User330639/ESP_SENSOR_STATION_REV1/HW/OUT/ASM/ASM_Top.PDF

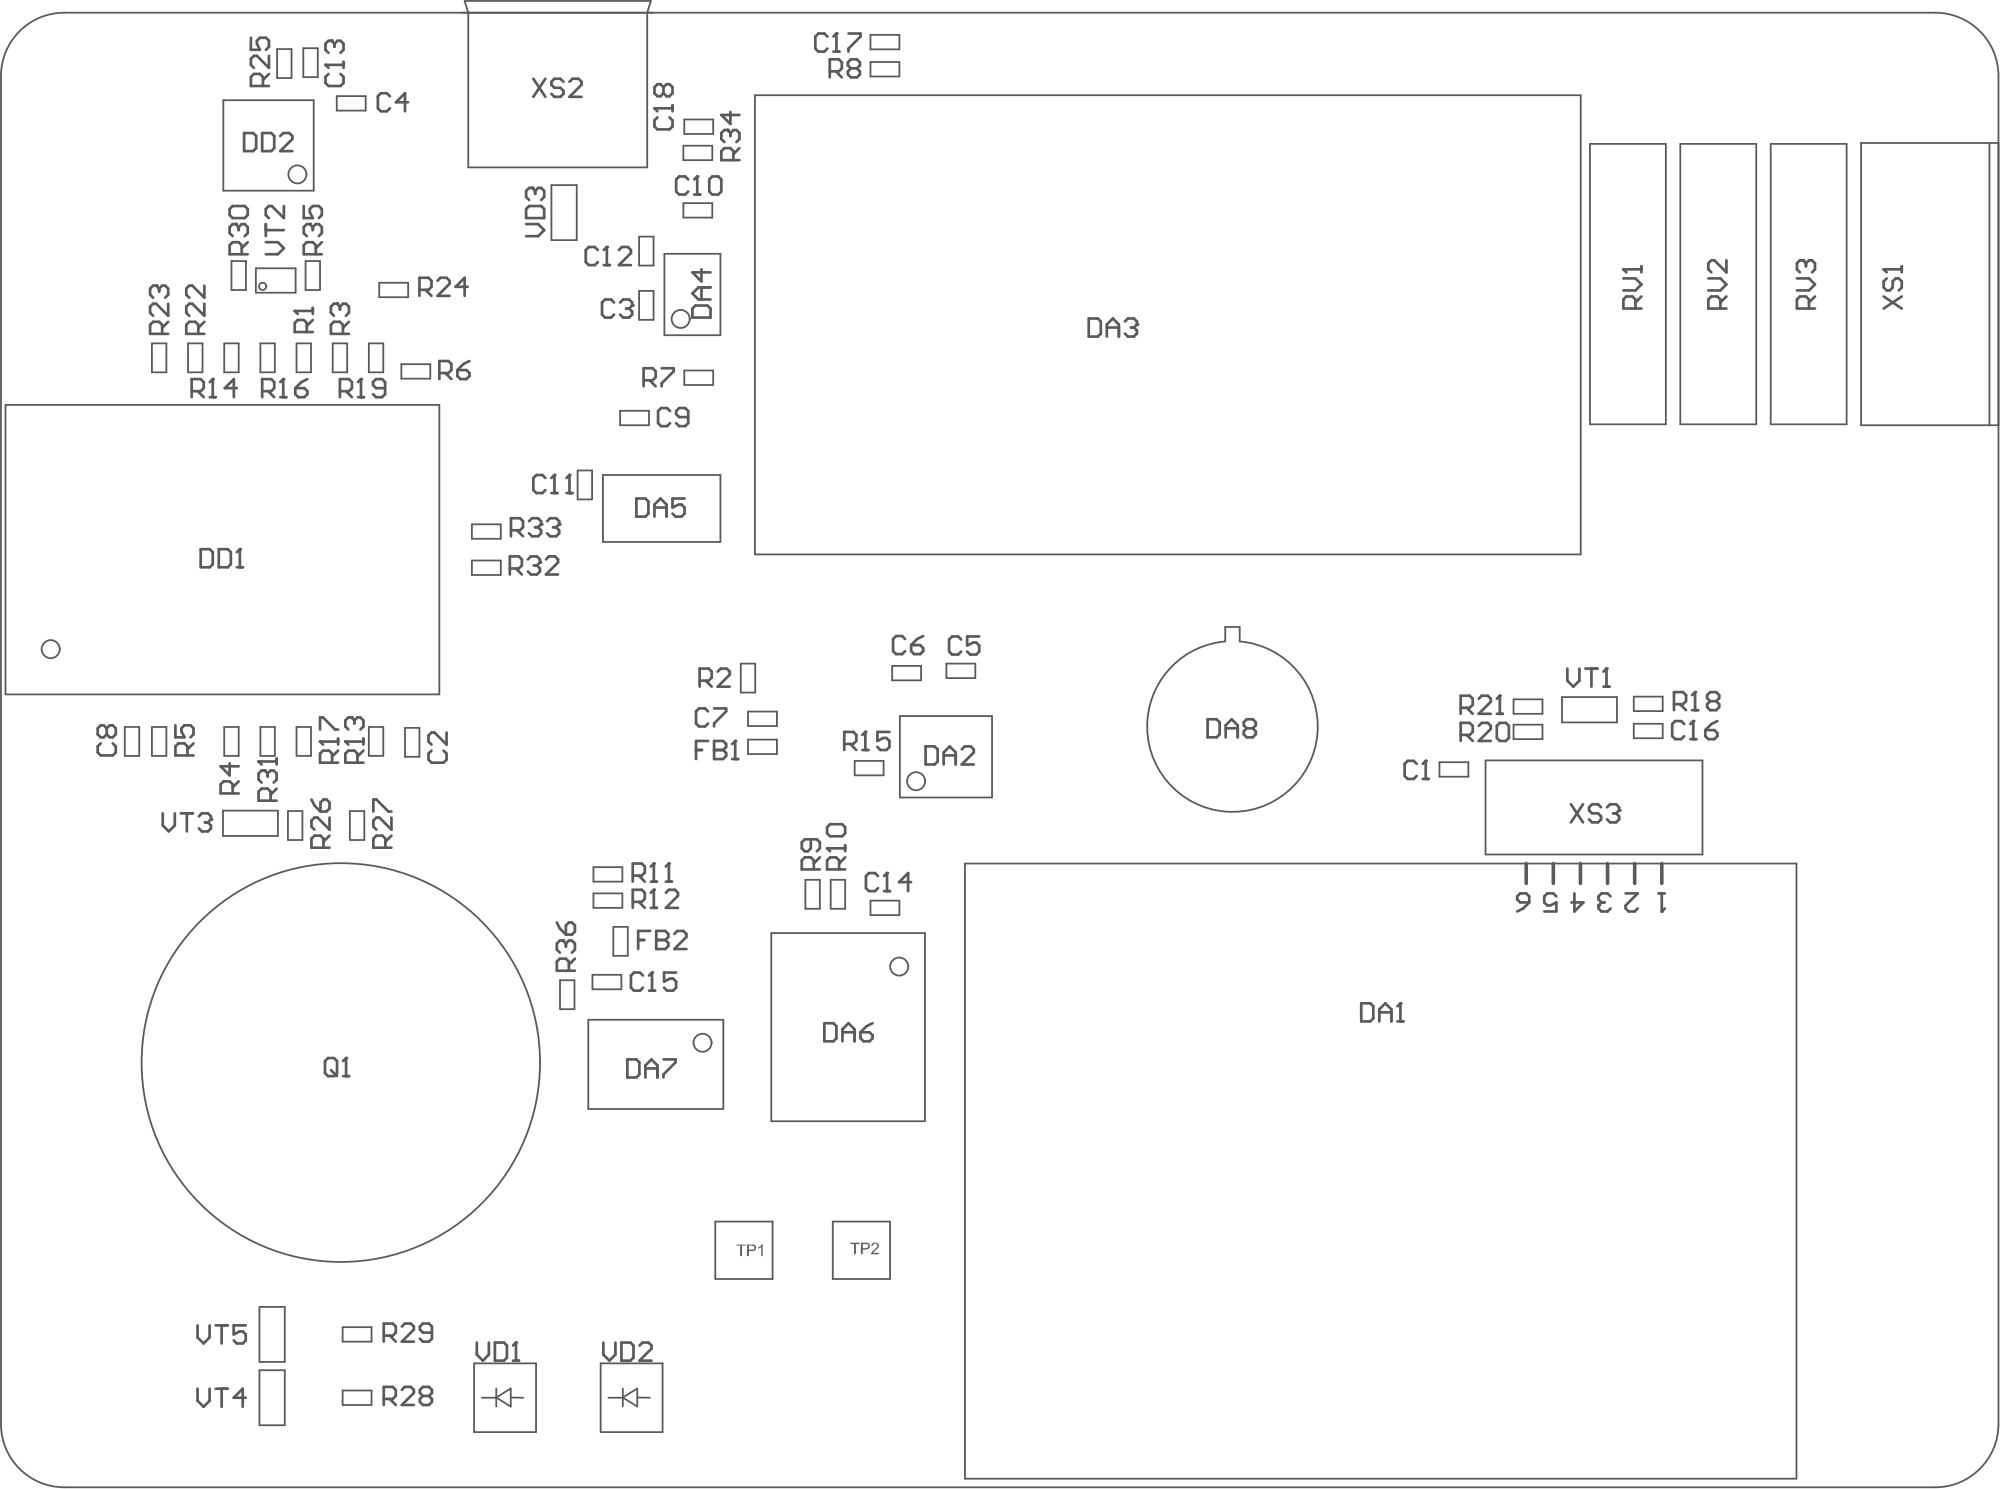
[picture p16: page 1]
