User330639/ESP_SENSOR_STATION_REV1/HW/OUT/PCB/PCB_Layers.PDF

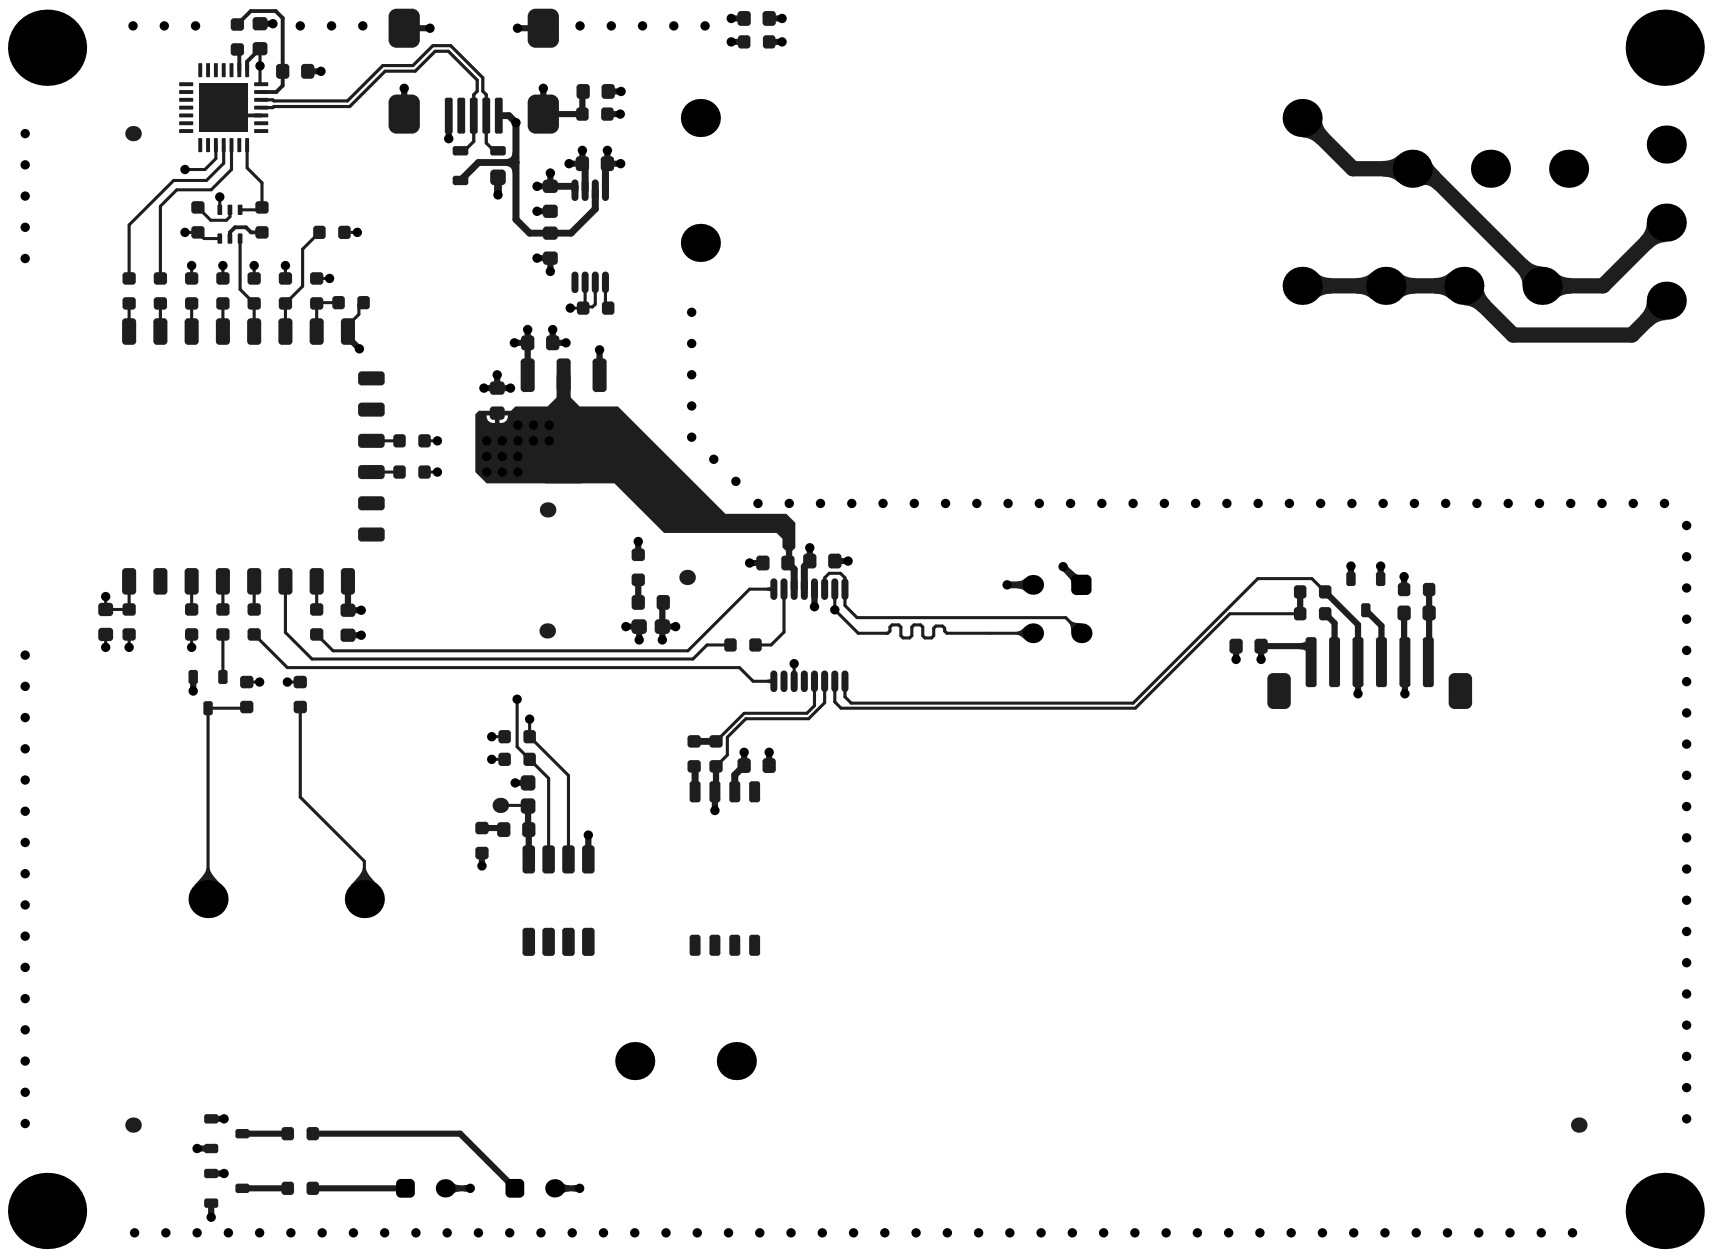
[picture p17: page 1]

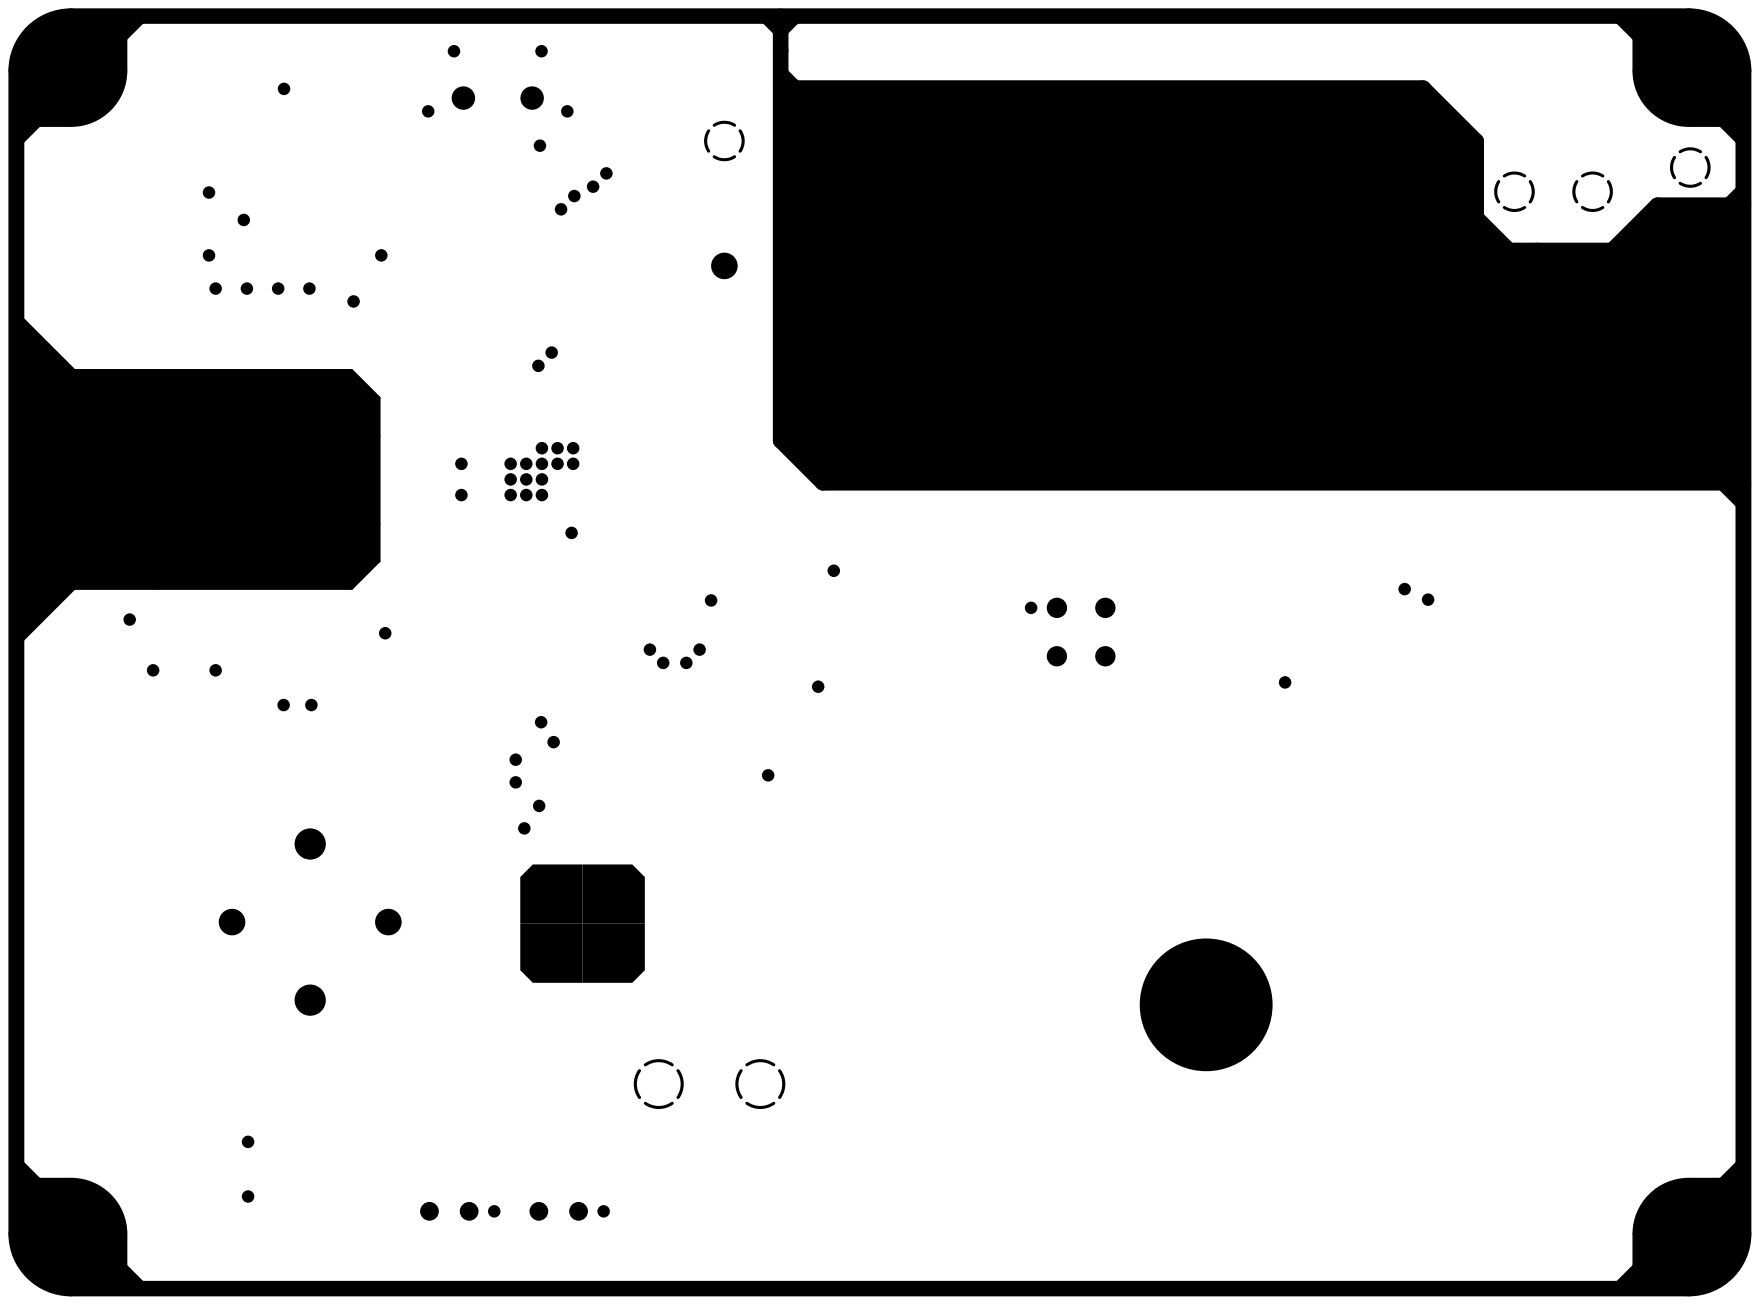
[picture p18: page 2]

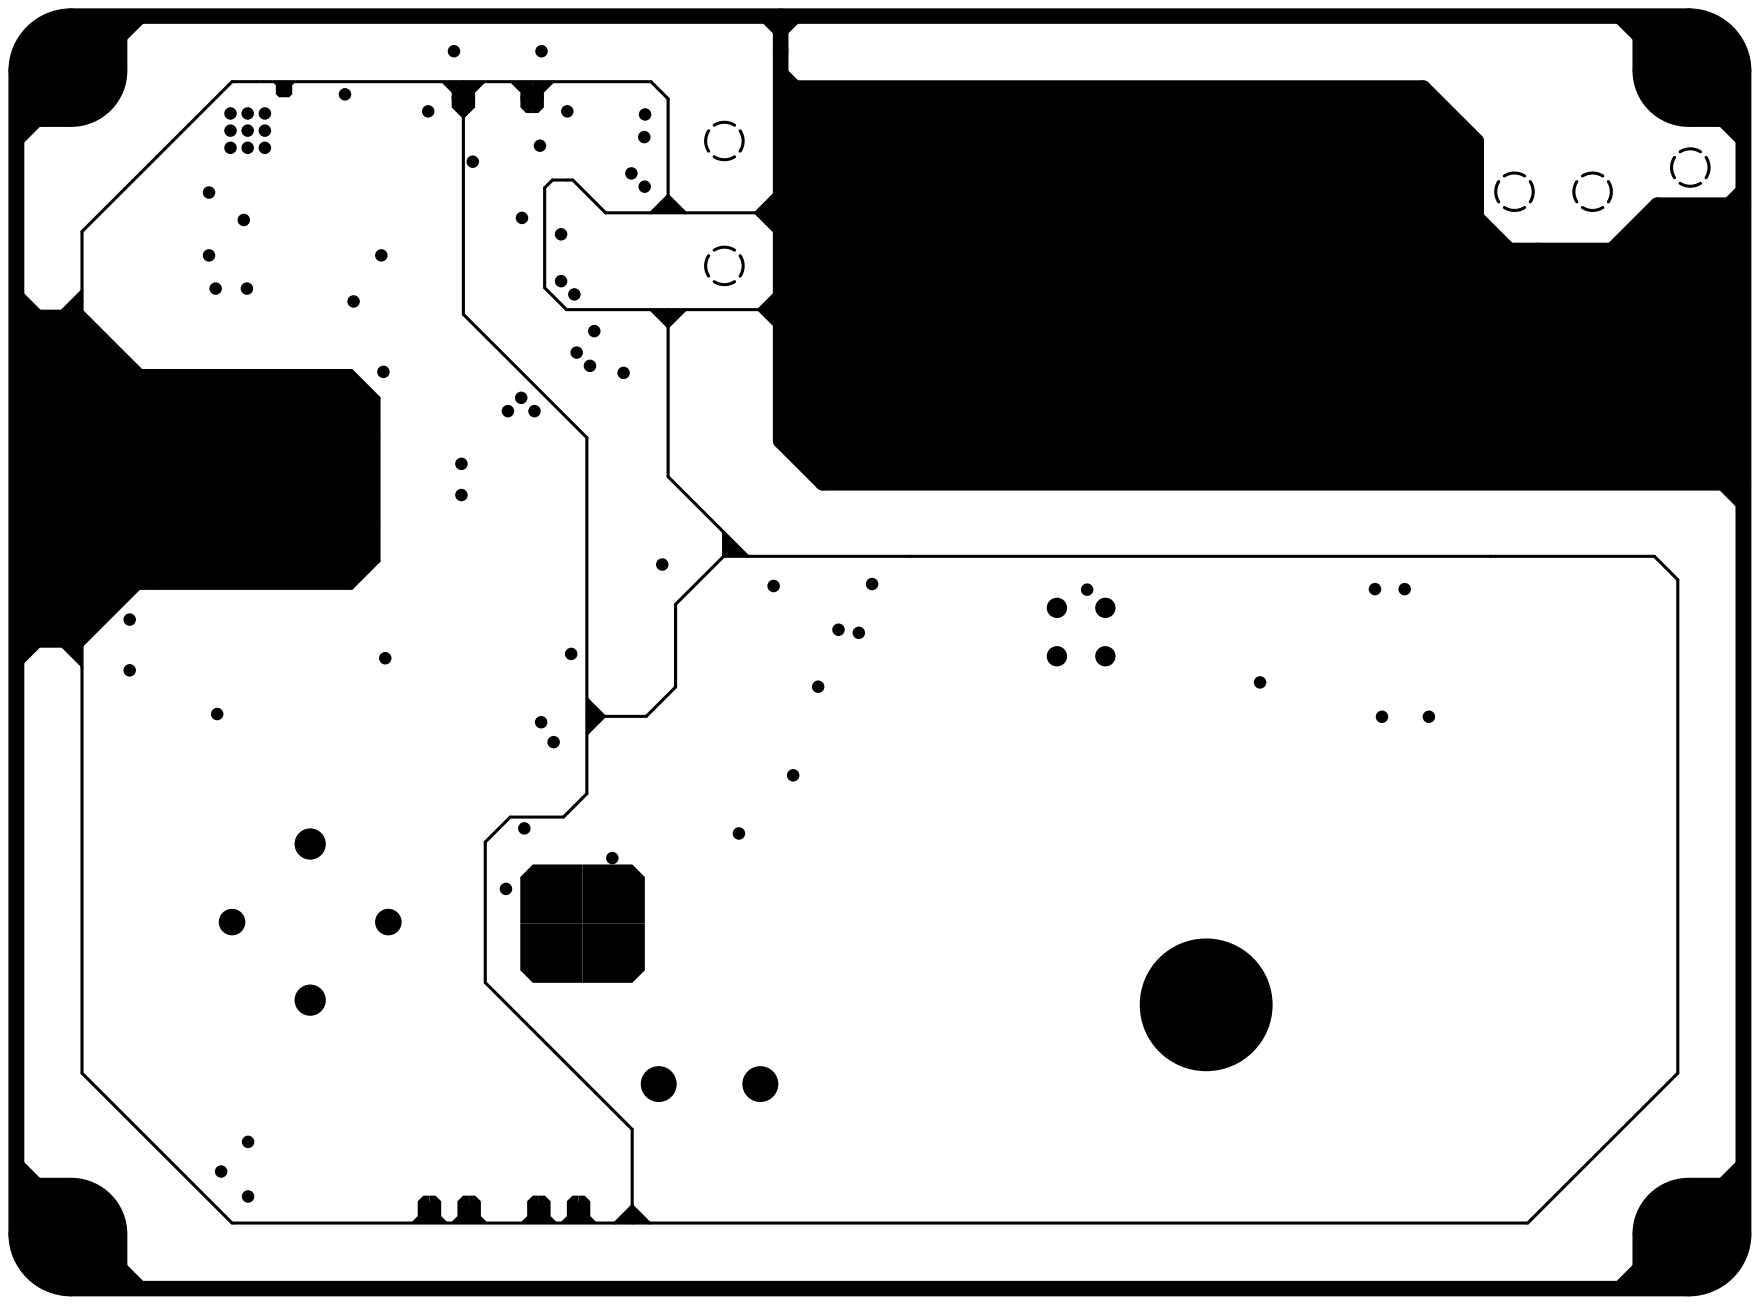
[picture p19: page 3]

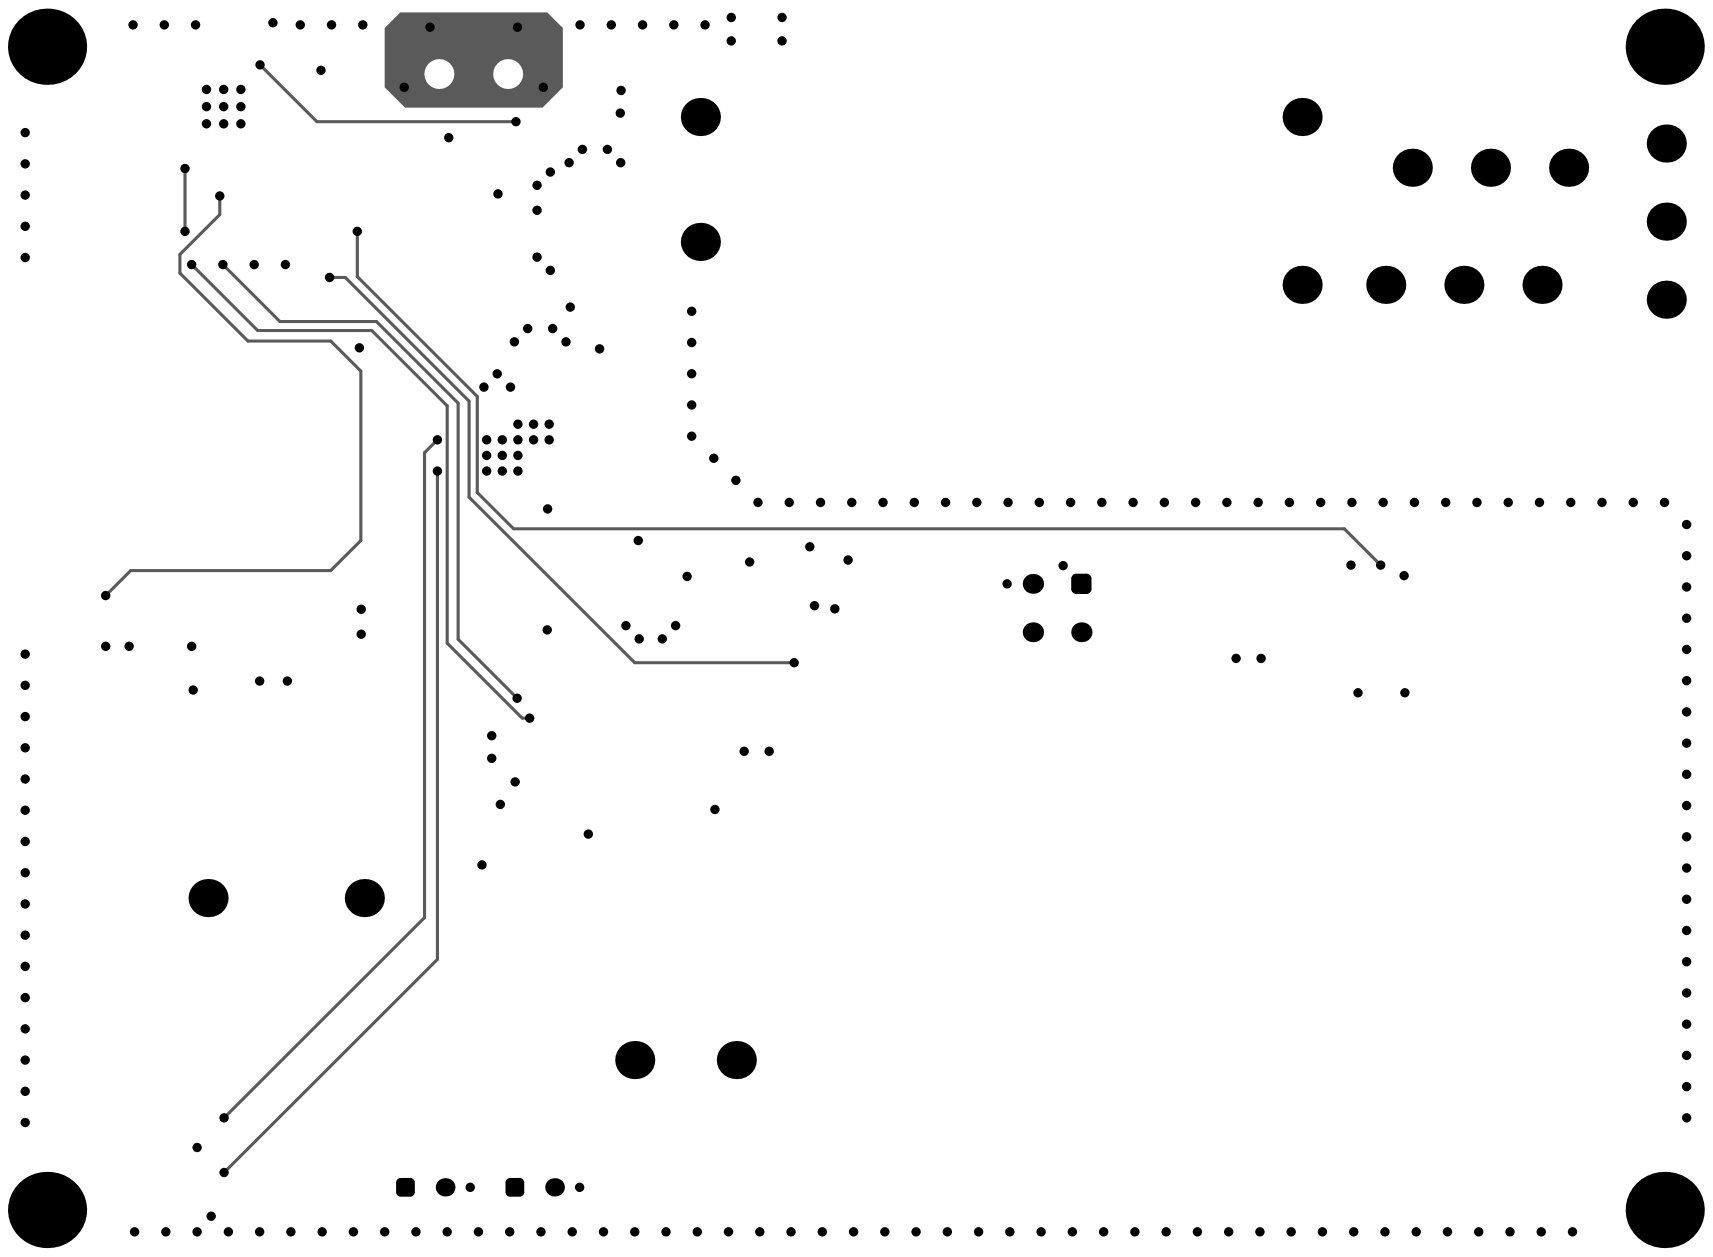
[picture p20: page 4]
